tedjelmoulksn-dotcom/Maison_a_basse_consommation/assets/maquette_assemblage_bois.jpg

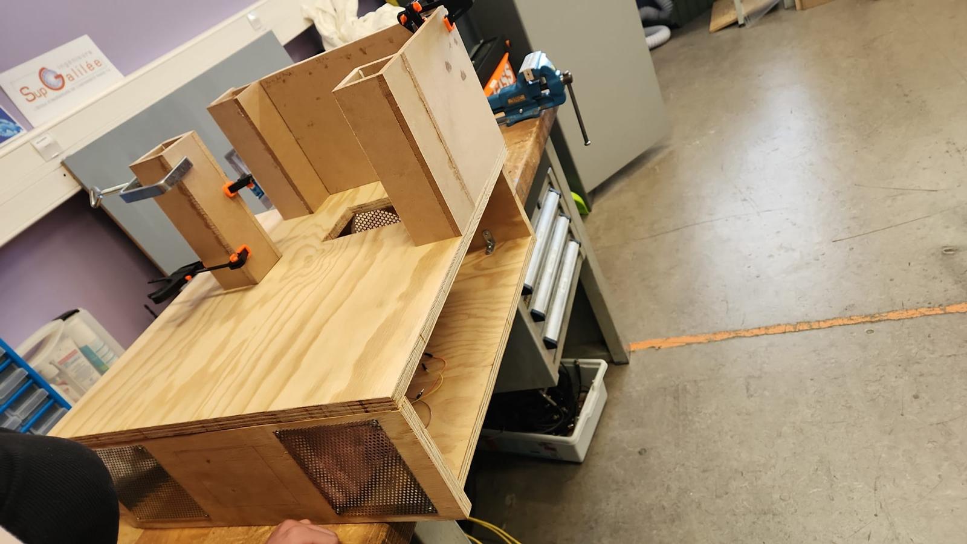
assets/maquette_assemblage_bois.jpg
